ufukcicekdev/ESP32_Nes_EMULATOR/nes_emulator/src/core/bus.h

#ifndef BUS_H
#define BUS_H

#include <Arduino.h>
#include <TFT_eSPI.h>
#include <stdio.h>
#include <stdint.h>
#include "config.h"
#include "cartridge.h"
#include "cpu6502.h"
#include "ppu2C02.h"

class Bus
{
public:
    Bus();
    ~Bus();

public:
    Cpu6502 cpu;
    Ppu2C02 ppu;
    Cartridge* cart = nullptr; // Başlangıçta boş
    uint8_t RAM[2048];
    uint8_t controller;

    // İşlemci Haberleşmesi
    void cpuWrite(uint16_t addr, uint8_t data);
    uint8_t cpuRead(uint16_t addr);
    
    // PPU ve Ekran Ayarları
    void setPPUMirrorMode(Cartridge::MIRROR mirror);
    Cartridge::MIRROR getPPUMirrorMode();

    void insertCartridge(Cartridge* cartridge);
    void connectScreen(TFT_eSPI* screen); // Ekranı bağlama fonksiyonu
    
    // Emülatör Kontrolü
    void reset();
    void clock();
    void IRQ();
    void NMI();
    void OAM_Write(uint8_t addr, uint8_t data);
    
    uint16_t ppu_scanline = 0;
    
    // PPU'nun hazırladığı 8 satırlık paketi ekrana basan fonksiyon
    void renderImage(uint16_t scanline);

    // Kayıt Fonksiyonları
    void saveState();
    void loadState();

private:
    void cpuClock();
    TFT_eSPI* ptr_screen = nullptr; // Ekranın hafıza adresi burada tutulur
    uint8_t controller_state;
    uint8_t controller_strobe = 0x00;
    bool frame_latch = false;
};

#endif
